CE-GPP/miniature-park/device/fabrication/8.5.dxf

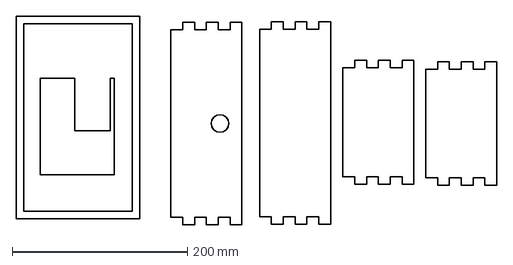
[picture p20: CAD file, 2023-03-10]
device/fabrication/8.5.dxf
547.9 x 237.8 mm
