CE-GPP/miniature-park/device/prototype models/prusa/holder2.3mf

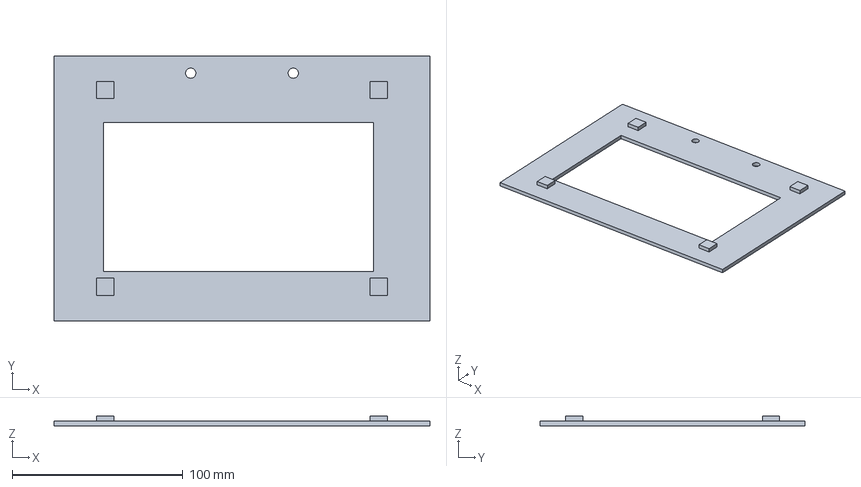
[picture p21: CAD file, 2023-03-02, an earlier design]
device/prototype models/prusa/holder2.3mf
220.0 x 155.0 x 6.00 mm
