CE-GPP/miniature-park/device/prototype models/container.stl

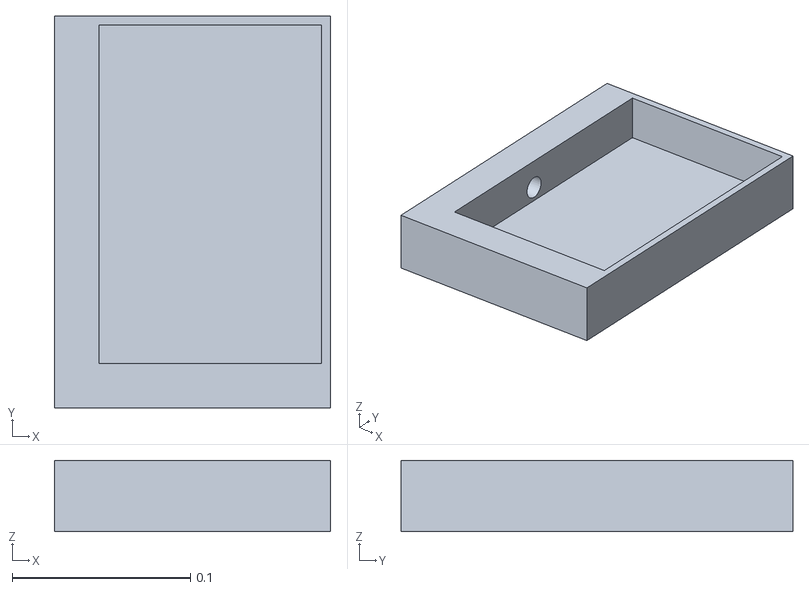
[picture p22: CAD file, 2023-02-28, an earlier design]
device/prototype models/container.stl
0.155 x 0.22 x 0.04
